karrister/Bluetooth-remote/Firmware/bt_remote.X/pic_config_bits.h

/* 
 * File:   pic_config_bits.h
 * Author: karrister
 *
 * Created on 27. kesäkuuta 2015, 20:31
 */

#ifndef PIC_CONFIG_BITS_H
#define	PIC_CONFIG_BITS_H

#ifdef	__cplusplus
extern "C" {
#endif


#pragma config CONFIG1L = 1
    

#ifdef	__cplusplus
}
#endif

#endif	/* PIC_CONFIG_BITS_H */
