karrister/Bluetooth-remote/Firmware/bt_remote.X/stiga_hockey.h

/* 
 * File:   stiga_hockey.h
 * Author: karrister
 *
 * Created on 24. June 2015, 2:32
 */

#ifndef STIGA_HOCKEY_H
#define	STIGA_HOCKEY_H

#ifdef	__cplusplus
extern "C" {
#endif




#ifdef	__cplusplus
}
#endif

#endif	/* STIGA_HOCKEY_H */
